dinobaurier/omnitrix/Esp32/data/98.png

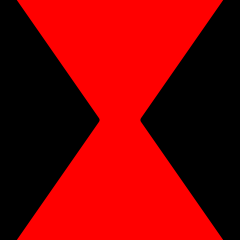
Esp32/data/98.png
