dinobaurier/omnitrix/Esp32/data/99.png

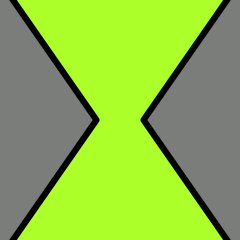
Esp32/data/99.png
