dinobaurier/omnitrix/Esp32/data/animation.gif

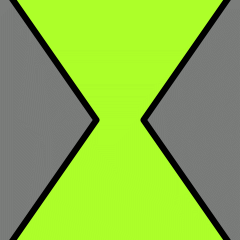
Esp32/data/animation.gif
