dinobaurier/omnitrix/Step/Lift Top v38.step

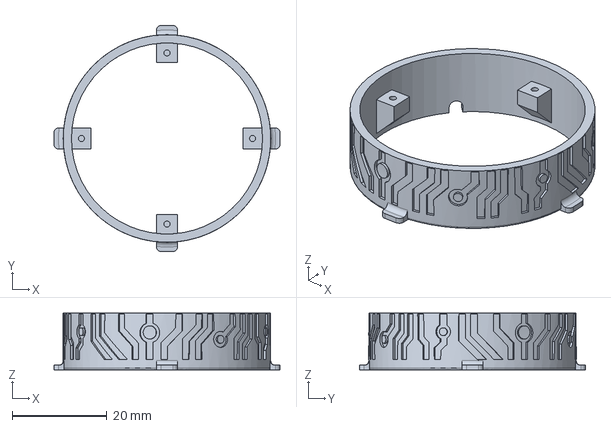
[picture p18: CAD file, 2022-01-10]
Step/Lift Top v38.step
47.7 x 47.7 x 12.0 mm
