dinobaurier/omnitrix/Step/Release Button v9.step

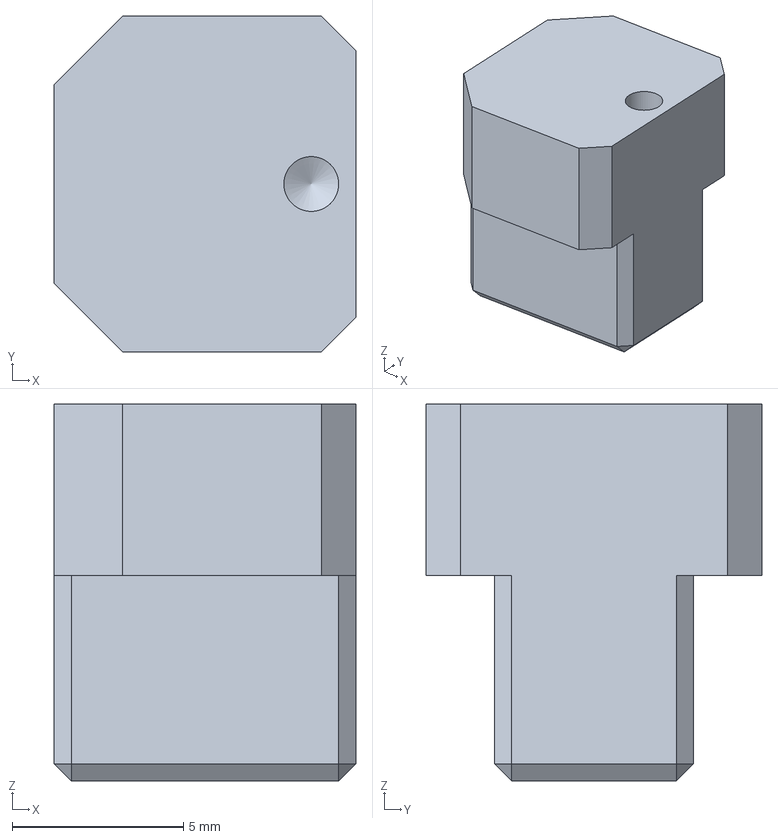
[picture p19: CAD file, 2022-01-10]
Step/Release Button v9.step
8.80 x 9.80 x 11.0 mm
