dinobaurier/omnitrix/Step/Glas v1.step

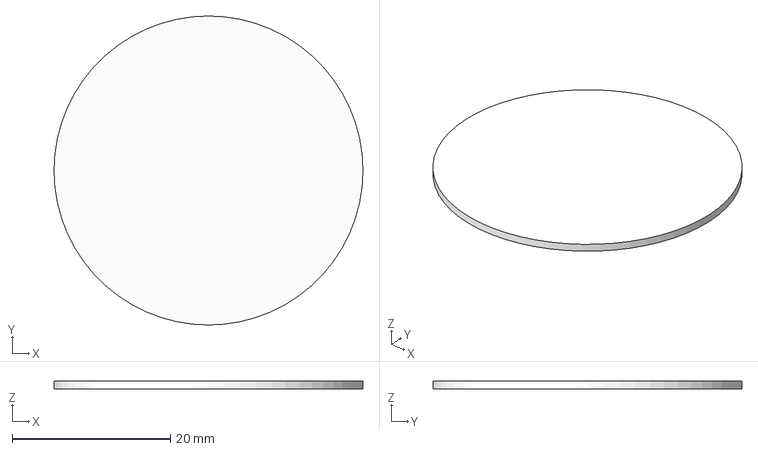
[picture p20: CAD file, 2022-01-10]
Step/Glas v1.step
39.0 x 39.0 x 1.00 mm
